MadhavGarg362006/Bit4Byte-K.R.A.M/Circuit/RadarDoppler.kicad_sch

## KiCad design Circuit/RadarDoppler.kicad_sch (2026-09-06)

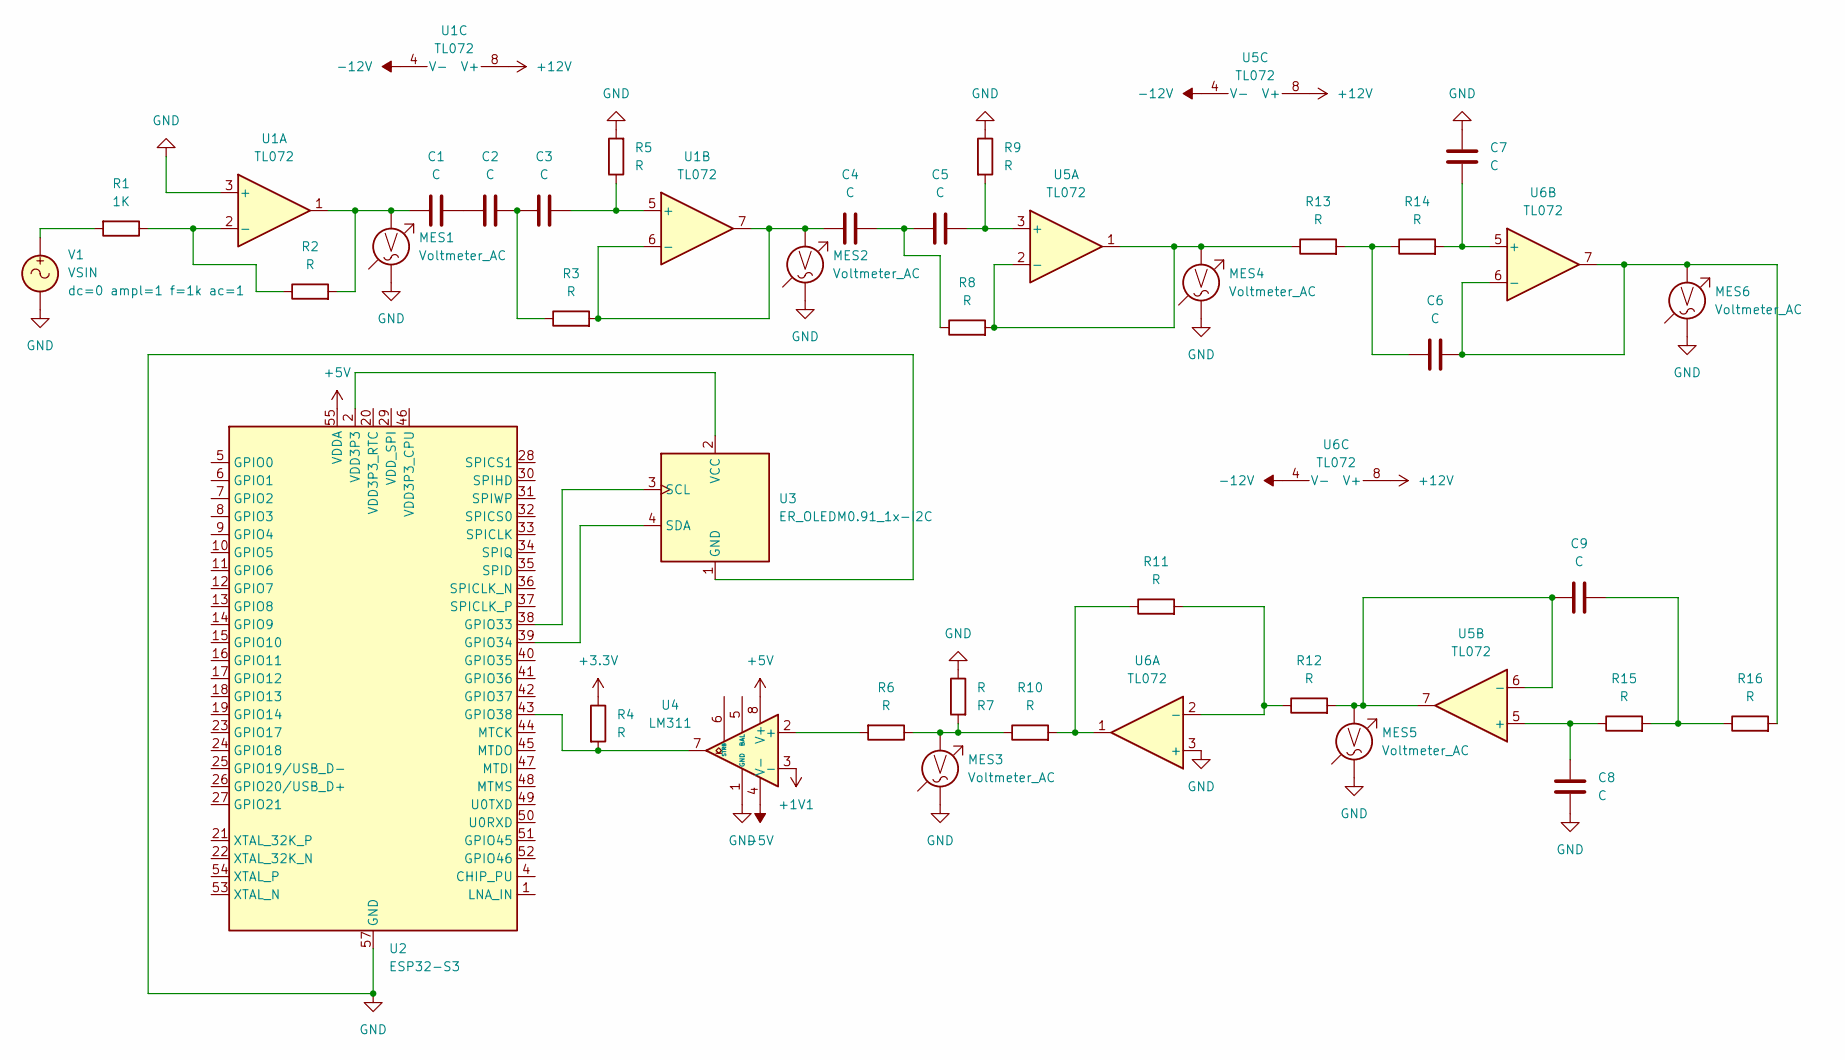
[picture p12: schematic RadarDoppler.kicad_sch]

Parts:
C1, C2, C3, C4, C5, C6, C7, C8, C9: C; SOIC-8_3.9x4.9mm_P1.27mm
MES1, MES2, MES3, MES4, MES5, MES6: Voltmeter_AC
R1: 1K; DIP-8_W7.62mm
R2, R3, R4, R5, R6, R7, R8, R9, R10, R11, R12, R13, R14, R15, R16: R; DIP-8_W7.62mm
U1, U5: TL072
U2: ESP32-S3; QFN-56-1EP_7x7mm_P0.4mm_EP4x4mm
U3: ER_OLEDM0.91_1x-I2C
U4: LM311
U6: TL072; Texas_DSQ0010A_WSON-10-1EP_2x2mm_P0.4mm_EP0.9x1.5mm
V1: VSIN; TQFP-44_10x10mm_P0.8mm

Connections:
+1V1: U4.3 (-)
+3.3V: R4.1
+5V: U2.55 (VDDA), U2.56 (VDDA), U4.8 (V+)
+12V: U1.8 (V+), U5.8 (V+), U6.8 (V+)
-5V: U4.4 (V-)
-12V: U1.4 (V-), U5.4 (V-), U6.4 (V-)
GND: C7.2, C8.2, MES1.1, MES2.1, MES3.1, MES4.1, MES5.1, MES6.1, R5.2, R7.1, R9.1, U1.3 (+), U2.57 (GND), U3.1 (GND), U4.1 (GND), U6.3 (+), V1.2
unnamed: C1.1, MES1.2, R2.2, U1.1
unnamed: C1.2, C2.1
unnamed: C2.2, C3.1, R3.1
unnamed: C3.2, R5.1, U1.5 (+)
unnamed: C4.1, MES2.2, R3.2, U1.6 (-), U1.7
unnamed: C4.2, C5.1, R8.1
unnamed: C5.2, R9.2, U5.3 (+)
unnamed: C6.1, R13.2, R14.1
unnamed: C6.2, MES6.2, R16.2, U6.6 (-), U6.7
unnamed: C7.1, R14.2, U6.5 (+)
unnamed: C8.1, R15.1, U5.5 (+)
unnamed: C9.1, MES5.2, R12.2, U5.6 (-), U5.7
unnamed: C9.2, R15.2, R16.1
unnamed: MES3.2, R6.1, R7.2, R10.1
unnamed: MES4.2, R8.2, R13.1, U5.1, U5.2 (-)
unnamed: R1.1, R2.1, U1.2 (-)
unnamed: R1.2, V1.1
unnamed: R4.2, U2.43 (GPIO38), U4.7
unnamed: R6.2, U4.2 (+)
unnamed: R10.2, R11.1, U6.1
unnamed: R11.2, R12.1, U6.2 (-)
unnamed: U2.2 (VDD3P3), U2.3 (VDD3P3), U3.2 (VCC)
unnamed: U2.38 (GPIO33), U3.3 (SCL)
unnamed: U2.39 (GPIO34), U3.4 (SDA)
